GoWired/GoWired-Project/Images/GetWired.png

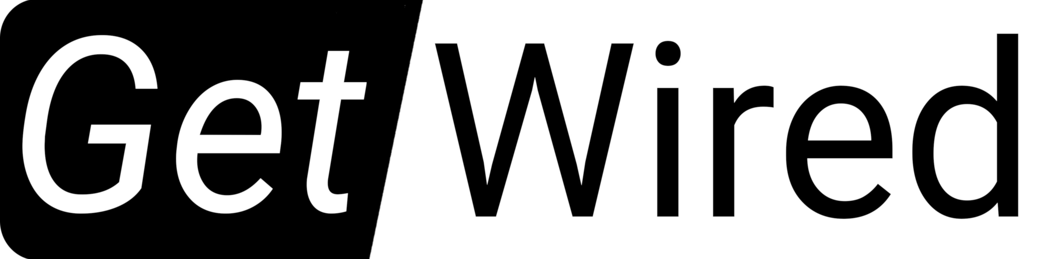
Images/GetWired.png
