GoWired/GoWired-Project/Images/Gowired-no-home-600dpi.png

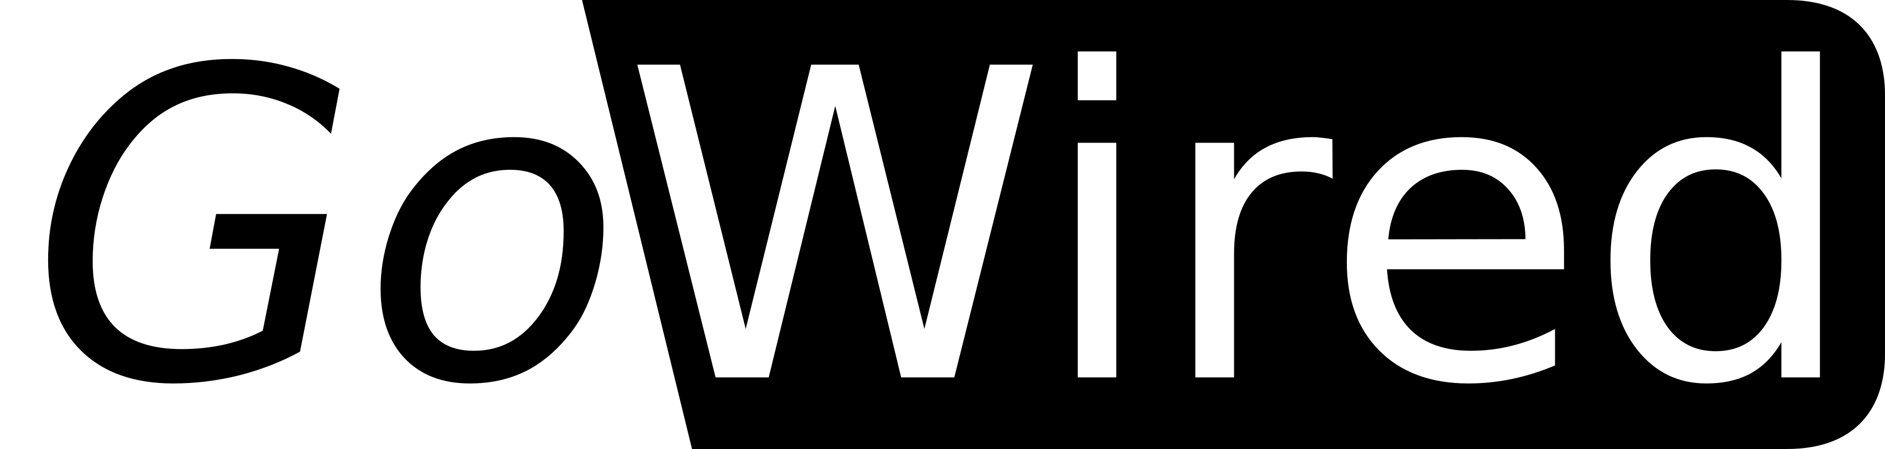
Images/Gowired-no-home-600dpi.png
