GoWired/GoWired-Project/Images/image.png

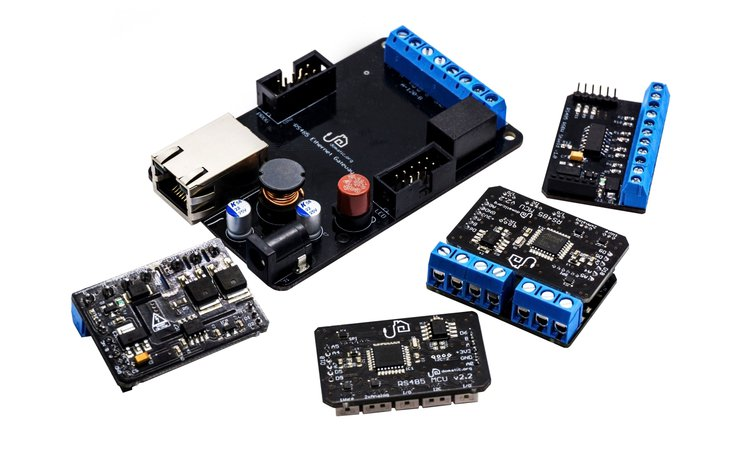
Images/image.png
