GoWired/GoWired-Project/Images/Wiring instructions.jpg

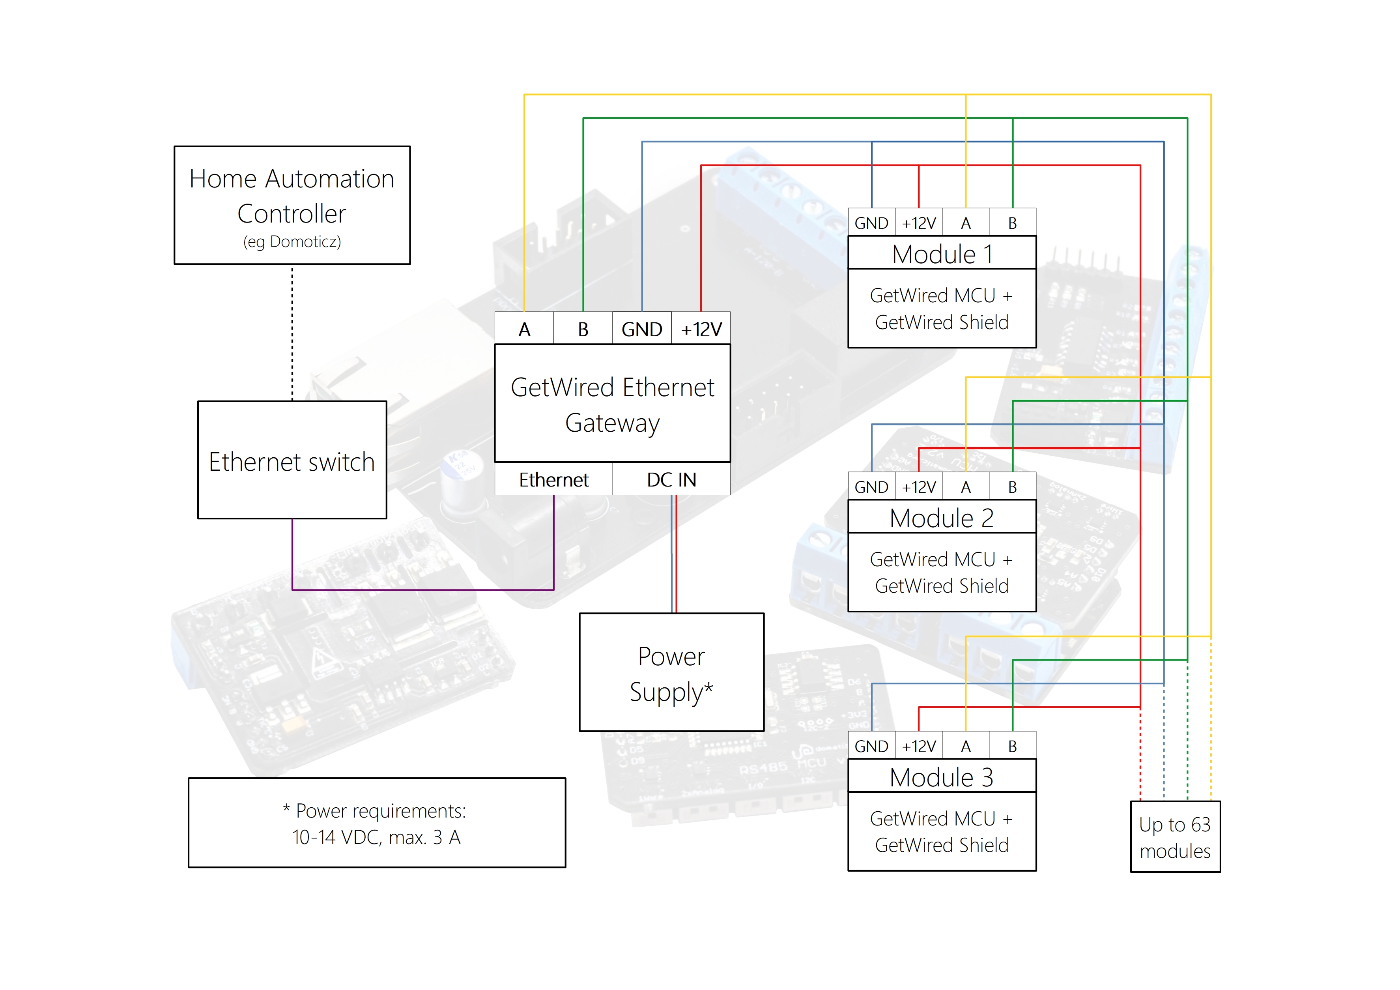
Images/Wiring instructions.jpg
