GoWired/GoWired-Project/Software/Modules/Arduino/main/main.ino

/*
 * GoWired is an open source project for WIRED home automation. It aims at making wired
 * home automation easy and affordable for every home automation enthusiast. GoWired provides
 * hardware, software, enclosures and instructions necessary to build your own bus communicating
 * smart home installation.
 * 
 * GoWired is based on RS485 industrial communication standard. The software uses MySensors
 * communication protocol (http://www.mysensors.org).
 *
 * Created by feanor-anglin
 * Copyright (C) 2018-2022 feanor-anglin
 *
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
 * ******************************
 * This is source code for GoWired MCU working with 2SSR, RGBW & 4RelayDin Shields.
 * 
 * 
 */

/***** INCLUDES *****/
#include "Configuration.h"
#include <GoWired.h>
#ifdef SHT30
  #include <SHTSensor.h>
#elif defined(DHT22)
  #include <dht.h>
#endif

/***** Globals *****/
// Shutter
#ifdef ROLLER_SHUTTER
  uint32_t MovementTime;
  uint32_t StartTime;
#endif

// Timer
uint32_t LastUpdate = 0;               // Time of last update of interval sensors
bool CheckNow = false;

// Module Safety Indicators
bool THERMAL_ERROR = false;                 // Thermal error status
bool InformControllerTS = false;            // Was controller informed about error?
bool OVERCURRENT_ERROR[4] = {false, false, false, false};             // Overcurrent error status
bool InformControllerES = false;            // Was controller informed about error?
uint8_t ET_ERROR = 3;                       // External thermometer status (0 - ok, 1 - checksum error, 2 - timeout error, 3 - default/initialization)

// Initialization
bool InitConfirm = false;

/***** Constructors *****/
// CommonIO constructor
#if (NUMBER_OF_RELAYS + NUMBER_OF_INPUTS > 0)
  CommonIO CommonIO[NUMBER_OF_RELAYS+NUMBER_OF_INPUTS];
#endif

MyMessage MsgSTATUS(0, V_STATUS);
MyMessage MsgPERCENTAGE(0, V_PERCENTAGE);
MyMessage MsgWATT(0, V_WATT);
MyMessage MsgTEMP(0, V_TEMP);
MyMessage MsgHUM(0, V_HUM);
MyMessage MsgTEXT(0, V_TEXT);

// Shutter Constructor
#ifdef ROLLER_SHUTTER
  Shutters Shutter(EEA_SHUTTER_TIME_DOWN, EEA_SHUTTER_TIME_UP, EEA_SHUTTER_POSITION);
  MyMessage MsgUP(SHUTTER_ID, V_UP);
  MyMessage MsgDOWN(SHUTTER_ID, V_DOWN);
  MyMessage MsgSTOP(SHUTTER_ID, V_STOP);
#endif

// Dimmer
#if defined(DIMMER) || defined(RGB) || defined(RGBW)
  Dimmer Dimmer;
  MyMessage MsgRGB(DIMMER_ID, V_RGB);
  MyMessage MsgRGBW(DIMMER_ID, V_RGBW);
#endif

// Power sensor constructor
#if defined(POWER_SENSOR) && !defined(FOUR_RELAY)
  PowerSensor PS;
#elif defined(POWER_SENSOR) && defined(FOUR_RELAY)
  PowerSensor PS[NUMBER_OF_RELAYS];
#endif

// Internal thermometer constructor
#ifdef INTERNAL_TEMP
  AnalogTemp AnalogTemp(IT_PIN, MAX_TEMPERATURE, MVPERC, ZEROVOLTAGE);
#endif

// External thermometer constructor
#ifdef EXTERNAL_TEMP
  #ifdef DHT22
    dht DHT;
  #endif
  #ifdef SHT30
    SHTSensor sht;
  #endif
#endif

#ifdef RS485_DEBUG
  MyMessage MsgDEBUG(DEBUG_ID, V_TEXT);
  MyMessage MsgDEBUG2(DEBUG_ID, V_WATT);
  MyMessage MsgCUSTOM(0, V_CUSTOM);
#endif

/**
 * @brief Function called before setup(); resets wdt
 * 
 */
void before() {

  #ifdef ENABLE_WATCHDOG
    wdt_reset();
    MCUSR = 0;
    wdt_disable();
  #endif
}

/**
 * @brief Setups software components: wdt, expander, inputs, outputs
 * 
 */
void setup() {

  #ifdef ENABLE_WATCHDOG
    wdt_enable(WDTO_8S);
  #endif

  float Vcc = ReadVcc();  // mV

  // POWER SENSOR
  #if defined(POWER_SENSOR) && !defined(FOUR_RELAY)
    PS.SetValues(PS_PIN, MVPERAMP, RECEIVER_VOLTAGE, MAX_CURRENT, POWER_MEASURING_TIME, Vcc);
  #elif defined(POWER_SENSOR) && defined(FOUR_RELAY)
    PS[RELAY_ID_1].SetValues(PS_PIN_1, MVPERAMP, RECEIVER_VOLTAGE, MAX_CURRENT, POWER_MEASURING_TIME, Vcc);
    PS[RELAY_ID_2].SetValues(PS_PIN_2, MVPERAMP, RECEIVER_VOLTAGE, MAX_CURRENT, POWER_MEASURING_TIME, Vcc);
    PS[RELAY_ID_3].SetValues(PS_PIN_3, MVPERAMP, RECEIVER_VOLTAGE, MAX_CURRENT, POWER_MEASURING_TIME, Vcc);
    PS[RELAY_ID_4].SetValues(PS_PIN_4, MVPERAMP, RECEIVER_VOLTAGE, MAX_CURRENT, POWER_MEASURING_TIME, Vcc);
  #endif

  // OUTPUT
  #ifdef DOUBLE_RELAY
    CommonIO[RELAY_ID_1].SetValues(RELAY_OFF, false, 4, BUTTON_1, RELAY_1);
    CommonIO[RELAY_ID_2].SetValues(RELAY_OFF, false, 4, BUTTON_2, RELAY_2);
  #endif

  #ifdef ROLLER_SHUTTER
    Shutter.SetOutputs( RELAY_OFF, RELAY_1, RELAY_2);
    CommonIO[SHUTTER_ID].SetValues(RELAY_OFF, false, 3, BUTTON_1);
    CommonIO[SHUTTER_ID + 1].SetValues(RELAY_OFF, false, 3, BUTTON_2);
    if(!Shutter.Calibrated) {
      Shutter.Calibration(UP_TIME, DOWN_TIME);
    }
  #endif

  #ifdef FOUR_RELAY
    CommonIO[RELAY_ID_1].SetValues(RELAY_OFF, 2, RELAY_1);
    CommonIO[RELAY_ID_2].SetValues(RELAY_OFF, 2, RELAY_2);
    CommonIO[RELAY_ID_3].SetValues(RELAY_OFF, 2, RELAY_3);
    CommonIO[RELAY_ID_4].SetValues(RELAY_OFF, 2, RELAY_4);
  #endif

  #if defined(DIMMER) || defined(RGB) || defined(RGBW)
    CommonIO[0].SetValues(0, false, 3, BUTTON_1);
    CommonIO[1].SetValues(0, false, 3, BUTTON_2);
  #endif

  #ifdef DIMMER
    Dimmer.SetValues(NUMBER_OF_CHANNELS, DIMMING_STEP, DIMMING_INTERVAL, LED_PIN_1, LED_PIN_2, LED_PIN_3, LED_PIN_4);
  #elif defined(RGB)
    Dimmer.SetValues(NUMBER_OF_CHANNELS, DIMMING_STEP, DIMMING_INTERVAL, LED_PIN_1, LED_PIN_2, LED_PIN_3);
  #elif defined(RGBW)
    Dimmer.SetValues(NUMBER_OF_CHANNELS, DIMMING_STEP, DIMMING_INTERVAL, LED_PIN_1, LED_PIN_2, LED_PIN_3, LED_PIN_4);
  #endif

  // INPUT
  #ifdef INPUT_1
    #ifdef PULLUP_1
      CommonIO[INPUT_ID_1].SetValues(RELAY_OFF, INVERT_1, 0, PIN_1);
    #else
      CommonIO[INPUT_ID_1].SetValues(RELAY_OFF, INVERT_1, 1, PIN_1);
    #endif
  #endif

  #ifdef INPUT_2
    #ifdef PULLUP_2
      CommonIO[INPUT_ID_2].SetValues(RELAY_OFF, INVERT_2, 0, PIN_2);
    #else
      CommonIO[INPUT_ID_2].SetValues(RELAY_OFF, INVERT_2, 1, PIN_2);
    #endif
  #endif

  #ifdef INPUT_3
    #ifdef PULLUP_3
      CommonIO[INPUT_ID_3].SetValues(RELAY_OFF, INVERT_3, 0, PIN_3);
    #else
      CommonIO[INPUT_ID_3].SetValues(RELAY_OFF, INVERT_3, 1, PIN_3);
    #endif
  #endif

  #ifdef INPUT_4
    #ifdef PULLUP_4
      CommonIO[INPUT_ID_4].SetValues(RELAY_OFF, INVERT_4, 0, PIN_4);
    #else
      CommonIO[INPUT_ID_4].SetValues(RELAY_OFF, INVERT_4, 1, PIN_4);
    #endif
  #endif

  // EXTERNAL THERMOMETER
  #ifdef EXTERNAL_TEMP
    #ifdef DHT22
      pinMode(ET_PIN, INPUT);
    #endif
    #ifdef SHT30
      Wire.begin();
      sht.init();
      sht.setAccuracy(SHTSensor::SHT_ACCURACY_MEDIUM);
    #endif
  #endif

}

/**
 * @brief Presents module to the controller, send name, software version, info about sensors
 * 
 */
void presentation() {

  sendSketchInfo(SN, SV);

  // OUTPUT
  #ifdef DOUBLE_RELAY
    present(RELAY_ID_1, S_BINARY, "Relay 1");   wait(PRESENTATION_DELAY);
    present(RELAY_ID_2, S_BINARY, "Relay 2");   wait(PRESENTATION_DELAY);
  #endif

  #ifdef ROLLER_SHUTTER
    present(SHUTTER_ID, S_COVER, "Roller Shutter");  wait(PRESENTATION_DELAY);
  #endif

  #ifdef FOUR_RELAY
    present(RELAY_ID_1, S_BINARY, "Relay 1");   wait(PRESENTATION_DELAY);
    present(RELAY_ID_2, S_BINARY, "Relay 2");   wait(PRESENTATION_DELAY);
    present(RELAY_ID_3, S_BINARY, "Relay 3");   wait(PRESENTATION_DELAY);
    present(RELAY_ID_4, S_BINARY, "Relay 4");   wait(PRESENTATION_DELAY);
  #endif

  #ifdef DIMMER
    present(DIMMER_ID, S_DIMMER, "Dimmer"); wait(PRESENTATION_DELAY);
  #endif

  #ifdef RGB
    present(DIMMER_ID, S_RGB_LIGHT, "RGB"); wait(PRESENTATION_DELAY);
  #endif

  #ifdef RGBW
    present(DIMMER_ID, S_RGBW_LIGHT, "RGBW");   wait(PRESENTATION_DELAY);
  #endif

  // DIGITAL INPUT
  #ifdef INPUT_1
    present(INPUT_ID_1, S_BINARY, "Input 1");   wait(PRESENTATION_DELAY);
  #endif

  #ifdef INPUT_2
    present(INPUT_ID_2, S_BINARY, "Input 2");   wait(PRESENTATION_DELAY);
  #endif

  #ifdef INPUT_3
    present(INPUT_ID_3, S_BINARY, "Input 3");   wait(PRESENTATION_DELAY);
  #endif

  #ifdef INPUT_4
    present(INPUT_ID_4, S_BINARY, "Input 4");   wait(PRESENTATION_DELAY);
  #endif

  #ifdef SPECIAL_BUTTON
    present(SPECIAL_BUTTON_ID, S_BINARY, "Longpress-1"); wait(PRESENTATION_DELAY);
    present(SPECIAL_BUTTON_ID+1, S_BINARY, "Longpress-2"); wait(PRESENTATION_DELAY);
  #endif

  // POWER SENSOR
  #if defined(POWER_SENSOR) && !defined(FOUR_RELAY)
    present(PS_ID, S_POWER, "Power Sensor");    wait(PRESENTATION_DELAY);
  #elif defined(POWER_SENSOR) && defined(FOUR_RELAY)
    present(PS_ID_1, S_POWER, "Power Sensor 1");    wait(PRESENTATION_DELAY);
    present(PS_ID_2, S_POWER, "Power Sensor 2");    wait(PRESENTATION_DELAY);
    present(PS_ID_3, S_POWER, "Power Sensor 3");    wait(PRESENTATION_DELAY);
    present(PS_ID_4, S_POWER, "Power Sensor 4");    wait(PRESENTATION_DELAY);
  #endif

  // Internal Thermometer
  #ifdef INTERNAL_TEMP
    present(IT_ID, S_TEMP, "Internal Thermometer"); wait(PRESENTATION_DELAY);
  #endif

  // External Thermometer
  #ifdef EXTERNAL_TEMP
    present(ETT_ID, S_TEMP, "External Thermometer"); wait(PRESENTATION_DELAY);
    present(ETH_ID, S_HUM, "External Hygrometer");  wait(PRESENTATION_DELAY);
  #endif

  // I2C


  // Error Reporting
  #ifdef ERROR_REPORTING
    #ifdef POWER_SENSOR
      present(ES_ID, S_BINARY, "OVERCURRENT ERROR");    wait(PRESENTATION_DELAY);
    #endif
    #ifdef INTERNAL_TEMP
      present(TS_ID, S_BINARY, "THERMAL ERROR");    wait(PRESENTATION_DELAY);
    #endif
    #ifdef EXTERNAL_TEMP
      present(ETS_ID, S_BINARY, "ET STATUS");   wait(PRESENTATION_DELAY);
    #endif
  #endif

  #ifdef RS485_DEBUG
    present(DEBUG_ID, S_INFO, "DEBUG INFO");
  #endif

  // Configuration sensor
  present(CONFIGURATION_SENSOR_ID, S_INFO, "TEXT Msg");

}

/**
 * @brief Sends initial value of sensors as required by Home Assistant
 * 
 */
void InitConfirmation() {

  // OUTPUT
  #ifdef DOUBLE_RELAY
    send(MsgSTATUS.setSensor(RELAY_ID_1).set(CommonIO[RELAY_ID_1].NewState));
    request(RELAY_ID_1, V_STATUS);
    wait(2000, C_SET, V_STATUS);

    send(MsgSTATUS.setSensor(RELAY_ID_2).set(CommonIO[RELAY_ID_2].NewState));
    request(RELAY_ID_2, V_STATUS);
    wait(2000, C_SET, V_STATUS);
  #endif

  #ifdef ROLLER_SHUTTER
    send(MsgUP.set(0));
    request(SHUTTER_ID, V_UP);
    wait(2000, C_SET, V_UP);

    send(MsgDOWN.set(0));
    request(SHUTTER_ID, V_DOWN);
    wait(2000, C_SET, V_DOWN);

    send(MsgSTOP.set(0));
    request(SHUTTER_ID, V_STOP);
    wait(2000, C_SET, V_STOP);

    send(MsgPERCENTAGE.setSensor(SHUTTER_ID).set(Shutter.Position));
    request(SHUTTER_ID, V_PERCENTAGE);
    wait(2000, C_SET, V_PERCENTAGE);
  #endif

  #ifdef FOUR_RELAY
    send(MsgSTATUS.setSensor(RELAY_ID_1).set(CommonIO[RELAY_ID_1].NewState));
    request(RELAY_ID_1, V_STATUS);
    wait(2000, C_SET, V_STATUS);
    
    send(MsgSTATUS.setSensor(RELAY_ID_2).set(CommonIO[RELAY_ID_2].NewState));
    request(RELAY_ID_2, V_STATUS);
    wait(2000, C_SET, V_STATUS);
    
    send(MsgSTATUS.setSensor(RELAY_ID_3).set(CommonIO[RELAY_ID_3].NewState));
    request(RELAY_ID_3, V_STATUS);
    wait(2000, C_SET, V_STATUS);
    
    send(MsgSTATUS.setSensor(RELAY_ID_4).set(CommonIO[RELAY_ID_4].NewState));
    request(RELAY_ID_4, V_STATUS);
    wait(2000, C_SET, V_STATUS);
  #endif

  #if defined(DIMMER) || defined(RGB) || defined(RGBW)
    send(MsgSTATUS.setSensor(DIMMER_ID).set(false));
    request(DIMMER_ID, V_STATUS);
    wait(2000, C_SET, V_STATUS);
    
    send(MsgPERCENTAGE.setSensor(DIMMER_ID).set(Dimmer.NewDimmingLevel));
    request(DIMMER_ID, V_PERCENTAGE);
    wait(2000, C_SET, V_PERCENTAGE);
  #endif

  #ifdef RGB
    send(MsgRGB.setSensor(DIMMER_ID).set("ffffff"));
    request(DIMMER_ID, V_RGB);
    wait(2000, C_SET, V_RGB);
  #elif defined(RGBW)
    send(MsgRGBW.setSensor(DIMMER_ID).set("ffffffff"));
    request(DIMMER_ID, V_RGBW);
    wait(2000, C_SET, V_RGBW);
  #endif

  // DIGITAL INPUT
  #ifdef INPUT_1
    send(MsgSTATUS.setSensor(INPUT_ID_1).set(CommonIO[INPUT_ID_1].NewState));
  #endif

  #ifdef INPUT_2
    send(MsgSTATUS.setSensor(INPUT_ID_2).set(CommonIO[INPUT_ID_2].NewState));
  #endif

  #ifdef INPUT_3
    send(MsgSTATUS.setSensor(INPUT_ID_3).set(CommonIO[INPUT_ID_3].NewState));
  #endif

  #ifdef INPUT_4
    send(MsgSTATUS.setSensor(INPUT_ID_4).set(CommonIO[INPUT_ID_4].NewState));
  #endif

  #ifdef SPECIAL_BUTTON
    send(MsgSTATUS.setSensor(SPECIAL_BUTTON_ID).set(0));
    send(MsgSTATUS.setSensor(SPECIAL_BUTTON_ID+1).set(0));
  #endif

  // Built-in sensors
  #ifdef POWER_SENSOR
    #if !defined(FOUR_RELAY)
      send(MsgWATT.setSensor(PS_ID).set("0"));
    #elif defined(FOUR_RELAY)
      for(int i=PS_ID_1; i<=PS_ID_4; i++)  {
        send(MsgWATT.setSensor(i).set("0"));
      }
    #endif
  #endif

  #ifdef INTERNAL_TEMP
    send(MsgTEMP.setSensor(IT_ID).set((int)AnalogTemp.MeasureT(ReadVcc())));
  #endif

  // External sensors
  #ifdef EXTERNAL_TEMP
    ETUpdate();
  #endif

  // Error Reporting
  #ifdef ERROR_REPORTING
    #ifdef POWER_SENSOR
      send(MsgSTATUS.setSensor(ES_ID).set(0));
    #endif
    #ifdef INTERNAL_TEMP
      send(MsgSTATUS.setSensor(TS_ID).set(0));
    #endif
    #ifdef EXTERNAL_TEMP
      send(MsgSTATUS.setSensor(ETS_ID).set(0));
    #endif
  #endif

  #ifdef RS485_DEBUG
    send(MsgDEBUG.setSensor(DEBUG_ID).set("DEBUG MESSAGE"));
  #endif

  send(MsgTEXT.setSensor(CONFIGURATION_SENSOR_ID).set("CONFIG INIT"));

  InitConfirm = true;
}


/**
 * @brief Handles incoming messages
 * 
 * @param message incoming message data
 */
void receive(const MyMessage &message)  {
  
  if (message.type == V_STATUS) {
    #if defined(POWER_SENSOR) && defined(ERROR_REPORTING)
      if (message.sensor == ES_ID)  {
        for (int i = 0; i < 4; i++)  {
          OVERCURRENT_ERROR[i] = message.getBool();
        }
        InformControllerES = false;
      }
    #endif
    #if defined(INTERNAL_TEMP) && defined(ERROR_REPORTING)
      if (message.sensor == TS_ID)  {
        THERMAL_ERROR = message.getBool();
        if (THERMAL_ERROR == false)  {
          InformControllerTS = false;
        }
      }
    #endif
    #ifdef SPECIAL_BUTTON
      if (message.sensor == SPECIAL_BUTTON_ID || message.sensor == SPECIAL_BUTTON_ID+1)  {
        // Ignore this message
      }
    #endif
    #if defined(DIMMER) || defined(RGB) || defined(RGBW)
      if (message.sensor == DIMMER_ID) {
        Dimmer.ChangeState(message.getBool());
      }
    #endif
    #if defined(DOUBLE_RELAY)
      if (message.sensor == RELAY_ID_1 || message.sensor == RELAY_ID_2)  {
        if (!OVERCURRENT_ERROR[0] && !THERMAL_ERROR) {
          CommonIO[message.sensor].SetState(message.getBool());
          CommonIO[message.sensor].SetRelay();
        }
      }
    #endif
    #ifdef FOUR_RELAY
      if (message.sensor >= RELAY_ID_1 && message.sensor < NUMBER_OF_RELAYS) {
        for (int i = RELAY_ID_1; i < RELAY_ID_1 + NUMBER_OF_RELAYS; i++) {
          if (message.sensor == i) {
            if (!OVERCURRENT_ERROR[i] && !THERMAL_ERROR) {
              CommonIO[message.sensor].NewState = message.getBool();
              CommonIO[message.sensor].SetRelay();
            }
          }
        }
      }
    #endif
  }
  else if (message.type == V_PERCENTAGE) {
    #ifdef ROLLER_SHUTTER
      if(message.sensor == SHUTTER_ID) {
        int NewPosition = atoi(message.data);
        NewPosition = NewPosition > 100 ? 100 : NewPosition;
        NewPosition = NewPosition < 0 ? 0 : NewPosition;
        Shutter.NewState = 2;
        ShutterUpdate(0);
        MovementTime = Shutter.ReadNewPosition(NewPosition) * 10;
      }
    #endif
    #if defined(DIMMER) || defined(RGB) || defined(RGBW)
      if(message.sensor == DIMMER_ID) {
        Dimmer.NewDimmingLevel = atoi(message.data);
        Dimmer.NewDimmingLevel = Dimmer.NewDimmingLevel > 100 ? 100 : Dimmer.NewDimmingLevel;
        Dimmer.NewDimmingLevel = Dimmer.NewDimmingLevel < 0 ? 0 : Dimmer.NewDimmingLevel;
      }
    #endif
  }
  else if (message.type == V_RGB || message.type == V_RGBW) {
    #if defined(RGB) || defined(RGBW)
      if(message.sensor == DIMMER_ID) {
        const char *rgbvalues = message.getString();

        Dimmer.NewColorValues(rgbvalues);
      }
    #endif
  }
  else if(message.type == V_UP) {
    #ifdef ROLLER_SHUTTER
      if(message.sensor == SHUTTER_ID) {
        MovementTime = Shutter.ReadMessage(0) * 1000;
      }
    #endif
  }
  else if(message.type == V_DOWN) {
    #ifdef ROLLER_SHUTTER
      if(message.sensor == SHUTTER_ID) {
        MovementTime = Shutter.ReadMessage(1) * 1000;
      }
    #endif
  }
  else if(message.type == V_STOP) {
    #ifdef ROLLER_SHUTTER
      if(message.sensor == SHUTTER_ID) {
        MovementTime = Shutter.ReadMessage(2);
      }
    #endif
  }
  else if(message.type == V_TEXT) {
    // Configuration by message
    if(message.sensor == CONFIGURATION_SENSOR_ID)  {
      
      // Initialize strings and pointers
      char ReceivedPayload[10];
      char *RPaddr = ReceivedPayload;
      String RPstr = String(message.getString());

      // Turn String payload to char array and send back to the controller
      RPstr.toCharArray(ReceivedPayload, 10);
      send(MsgTEXT.setSensor(CONFIGURATION_SENSOR_ID).set(RPaddr));

      if(RPstr.equals(CONF_MSG_1)) {
        #ifdef ROLLER_SHUTTER
          // Roller shutter: calibration
          float Vcc = ReadVcc();
          ShutterCalibration(Vcc);
        #endif
      }
      else if(RPstr.equals(CONF_MSG_2)) {
        // No effect
      }
      else if(RPstr.equals(CONF_MSG_3)) {
        // Watchdog test procedure / module restart
        delay(10000);
      }
      else if(RPstr.equals(CONF_MSG_4)) {
        // Clear EEPROM and restart
        for (int i=0;i<1024;i++) {
          EEPROM.write(i,0xFF);
        }
        delay(10000);
      }
    }
  }
}

/**
 * @brief Reads temperature & humidity from an optional, external thermometer 
 * 
 */
void ETUpdate()  {

  #ifdef EXTERNAL_TEMP
    #ifdef DHT22
      int chk = DHT.read22(ET_PIN);
      switch (chk)  {
        case DHTLIB_OK:
          send(MsgTEMP.setSensor(ETT_ID).setDestination(0).set(DHT.temperature, 1));
          send(MsgHUM.setSensor(ETH_ID).set(DHT.humidity, 1));
          #ifdef HEATING_SECTION_SENSOR
            send(MsgTEMP.setSensor(ETT_ID).setDestination(MY_HEATING_CONTROLLER).set(DHT.temperature, 1));
          #endif
          #ifdef ERROR_REPORTING
            if (ET_ERROR != 0) {
              ET_ERROR = 0;
              send(MsgSTATUS.setSensor(ETS_ID).set(ET_ERROR));
            }
          #endif
        break;
        case DHTLIB_ERROR_CHECKSUM:
          #ifdef ERROR_REPORTING
            ET_ERROR = 1;
            send(MsgSTATUS.setSensor(ETS_ID).set(ET_ERROR));
          #endif
        break;
        case DHTLIB_ERROR_TIMEOUT:
          #ifdef ERROR_REPORTING
            ET_ERROR = 2;
            send(MsgSTATUS.setSensor(ETS_ID).set(ET_ERROR));
          #endif
        break;
        default:
          #ifdef ERROR_REPORTING
            ET_ERROR = 3;
            send(MsgSTATUS.setSensor(ETS_ID).set(ET_ERROR));
          #endif
        break;
      }
    #elif defined(SHT30)
      if(sht.readSample())  {
        send(MsgTEMP.setSensor(ETT_ID).setDestination(0).set(sht.getTemperature(), 1));
        send(MsgHUM.setSensor(ETH_ID).set(sht.getHumidity(), 1));
        #ifdef HEATING_SECTION_SENSOR
          send(MsgTEMP.setSensor(ETT_ID).setDestination(MY_HEATING_CONTROLLER).set(sht.getTemperature(), 1));
        #endif
      }
      else  {
        #ifdef ERROR_REPORTING
          ET_ERROR = 1;
          send(MsgSTATUS.setSensor(ETS_ID).set(ET_ERROR));
        #endif
      }
    #endif
  #endif
}

/**
 * @brief Updates CommonIO class objects; reads inputs & set outputs
 * 
 */
void UpdateIO() {

  int FirstSensor = 0;
  int Iterations = NUMBER_OF_RELAYS+NUMBER_OF_INPUTS;

  if(Iterations <= 0)  return;

  for (int i = FirstSensor; i < FirstSensor + Iterations; i++)  {
    CommonIO[i].CheckInput(LONGPRESS_DURATION, DEBOUNCE_VALUE);

    if (CommonIO[i].NewState == CommonIO[i].State)  continue;

    switch(CommonIO[i].SensorType)  {
      case 0:
        // Door/window/button
      case 1:
        // Motion sensor
        send(MsgSTATUS.setSensor(i).set(CommonIO[i].NewState));
        CommonIO[i].State = CommonIO[i].NewState;
        break;
      case 2:
        // Relay output
        // Nothing to do here
        break;
      case 3:
        // Button input
        #ifdef DIMMER_ID
          if(i == 0)  {
            if(CommonIO[i].NewState != 2) {
              // Change dimmer state
              Dimmer.ChangeState(!Dimmer.CurrentState);
              send(MsgSTATUS.setSensor(DIMMER_ID).set(Dimmer.CurrentState));
              CommonIO[i].State = CommonIO[i].NewState;
            }
            if(CommonIO[i].NewState == 2) {
              #ifdef SPECIAL_BUTTON
                send(MsgSTATUS.setSensor(SPECIAL_BUTTON_ID).set(true));
              #endif
              CommonIO[i].NewState = CommonIO[i].State;
            }
          }
          else if(i == 1) {
            if(CommonIO[i].NewState != 2)  {
              if(!Dimmer.CurrentState) continue;
                    
              // Toggle dimming level by DIMMING_TOGGLE_STEP
              Dimmer.NewDimmingLevel += DIMMING_TOGGLE_STEP;
              Dimmer.NewDimmingLevel = Dimmer.NewDimmingLevel > 100 ? DIMMING_TOGGLE_STEP : Dimmer.NewDimmingLevel;
              send(MsgPERCENTAGE.setSensor(DIMMER_ID).set(Dimmer.NewDimmingLevel));
              CommonIO[i].NewState = CommonIO[i].State;
            }
          }
        #endif
        #ifdef ROLLER_SHUTTER
          if(CommonIO[i].NewState != 2)  {
            MovementTime = Shutter.ReadButtons(i) * 1000;
            CommonIO[i].State = CommonIO[i].NewState;
          }
          else  {
            #ifdef SPECIAL_BUTTON
              send(MsgSTATUS.setSensor(SPECIAL_BUTTON_ID).set(true));
            #endif
            CommonIO[i].NewState = CommonIO[i].State;
          }
        #endif
        break;
      case 4:
        // Button input + Relay output
        if (CommonIO[i].NewState != 2)  {
          if (OVERCURRENT_ERROR[0] || THERMAL_ERROR)  continue;

          CommonIO[i].SetRelay();
          send(MsgSTATUS.setSensor(i).set(CommonIO[i].NewState));
        }
        else if (CommonIO[i].NewState == 2)  {
          #ifdef SPECIAL_BUTTON
            uint8_t SensorID = i == 0 ? SPECIAL_BUTTON_ID : SPECIAL_BUTTON_ID+1;
            send(MsgSTATUS.setSensor(SensorID).set(true));
          #endif
          
          CommonIO[i].NewState = CommonIO[i].State;
        }
        break;
      default:
        // Nothing to do here
        break;
    }
  }
}

/**
 * @brief Measures shutter movement duration; calls class Calibration() function to save measured durations
 * 
 * @param Vcc current uC voltage
 */
void ShutterCalibration(float Vcc)  {

  #ifdef ROLLER_SHUTTER

  float Current = 0;
  uint32_t DownTimeCumulated = 0;
  uint32_t UpTimeCumulated = 0;
  uint32_t StartTime = 0;
  uint32_t StopTime = 0;
  uint32_t MeasuredTime = 0;

  // Opening the shutter  
  Shutter.NewState = 0;
  Shutter.Movement();

  do  {
    delay(500);
    wdt_reset();
    Current = PS.MeasureAC(Vcc);
  } while(Current > PS_OFFSET);

  Shutter.NewState = 2;
  Shutter.Movement();

  delay(1000);

  // Calibrating
  for(int i=0; i<CALIBRATION_SAMPLES; i++) {
    for(int j=1; j>=0; j--)  {
      Shutter.NewState = j;
      Shutter.Movement();
      StartTime = millis();

      do  {
        delay(250);
        Current = PS.MeasureAC(Vcc);
        StopTime = millis();
        wdt_reset();
      } while(Current > PS_OFFSET);

      Shutter.NewState = 2;
      Shutter.Movement();

      MeasuredTime = StopTime - StartTime;

      if(j) {
        DownTimeCumulated += (int)(MeasuredTime / 1000);
      }
      else  {
        UpTimeCumulated += (int)(MeasuredTime / 1000);
      }

      delay(1000);
    }
  }

  Shutter.Position = 0;

  uint8_t DownTime = (int)(DownTimeCumulated / CALIBRATION_SAMPLES);
  uint8_t UpTime = (int)(UpTimeCumulated / CALIBRATION_SAMPLES);

  Shutter.Calibration(UpTime+1, DownTime+1);

  EEPROM.put(EEA_SHUTTER_TIME_DOWN, DownTime);
  EEPROM.put(EEA_SHUTTER_TIME_UP, UpTime);
  EEPROM.put(EEA_SHUTTER_POSITION, Shutter.Position);

  // Inform Controller about the current state of roller shutter
  send(MsgSTOP);
  send(MsgPERCENTAGE.setSensor(SHUTTER_ID).set(Shutter.Position));
  #ifdef RS485_DEBUG
    send(MsgDEBUG.set("DownTime ; UpTime"));
    send(MsgCUSTOM.set(DownTime)); send(MsgCUSTOM.set(UpTime));
  #endif

  #endif
    
}

/**
 * @brief Updates shutter condition, informs controller about shutter condition and position
 * 
 */
void ShutterUpdate(float Current) {

  #ifdef ROLLER_SHUTTER

  uint32_t StopTime = 0;
  uint32_t MeasuredTime;
  uint8_t TempState = 2;
  bool Direction;

  if(Shutter.State != 2) {
    if((millis() >= StartTime + MovementTime) || (Current < PS_OFFSET)) {
      StopTime = millis();
    }
    else if(millis() < StartTime)  {
      uint32_t Temp = 4294967295 - StartTime + millis();
      wait(MovementTime - Temp);
      StartTime = 0;
      StopTime = MovementTime;
    }
  }

  if(Shutter.State != Shutter.NewState) {
    if(Shutter.NewState != 2)  {
      if(Shutter.State == 2)  {
        ShutterStart();
      }
      else  {
        TempState = Shutter.NewState;
        StopTime = millis();
      }
    }
    else  {
      StopTime = millis();
    }
  }

  if(StopTime > 0)  {
    Direction = Shutter.State;
    Shutter.NewState = 2;
    Shutter.Movement();
    send(MsgSTOP.setSensor(SHUTTER_ID));

    MeasuredTime = StopTime - StartTime;
    Shutter.CalculatePosition(Direction, MeasuredTime);
    EEPROM.put(EEA_SHUTTER_POSITION, Shutter.Position);
  
    send(MsgPERCENTAGE.setSensor(SHUTTER_ID).set(Shutter.Position));
  
    if(TempState != 2)  {
      wait(500);
      Shutter.NewState = TempState;
      ShutterStart();
    }
  }
  #endif
}

void ShutterStart() {

  #ifdef ROLLER_SHUTTER

  Shutter.Movement();
  StartTime = millis();

  Shutter.NewState == 0 ? send(MsgUP.setSensor(SHUTTER_ID)) : send(MsgDOWN.setSensor(SHUTTER_ID));

  wait(500);

  #endif
}

/**
 * @brief Informs controller about power sensor readings
 * 
 * @param Current current measured by sensor 
 * @param Sensor sensor ID if more than one sensor is attached
 */
void PSUpdate(float Current, uint8_t Sensor = 0)  {

  if(Current == 0 && PS.OldValue == 0)  return;
  else if(Current < 1 && (abs(PS.OldValue - Current) < 0.1)) return;
  else if(Current >= 1 && (abs(PS.OldValue - Current) < (0.1 * PS.OldValue))) return;
  
  #if defined(POWER_SENSOR) && !defined(FOUR_RELAY)
    send(MsgWATT.setSensor(PS_ID).set(PS.CalculatePower(Current, COSFI), 0));
    PS.OldValue = Current;
  #elif defined(POWER_SENSOR) && defined(FOUR_RELAY)
    send(MsgWATT.setSensor(Sensor+4).set(PS[Sensor].CalculatePower(Current, COSFI), 0));
    PS[Sensor].OldValue = Current;
  #endif

}

/**
 * @brief Measures uC supply voltage
 * 
 * @return long measured voltage in mV
 */
long ReadVcc() {
  
  long result;
  
  // Read 1.1V reference against AVcc
  ADMUX = _BV(REFS0) | _BV(MUX3) | _BV(MUX2) | _BV(MUX1);
  
  delay(2);
  
  ADCSRA |= _BV(ADSC); // Convert
  
  while (bit_is_set(ADCSRA,ADSC));
  
  result = ADCL;
  result |= ADCH<<8;
  result = 1126400L / result; // Back-calculate AVcc in mV
  result = result;
  
  return result;
}

/**
 * @brief main loop: calls all 'Update' functions, runs all measurements, checks if safety parameters are within limits
 * 
 */
void loop() {

  float Vcc = ReadVcc(); // mV
  float Current = 0;

  // Sending out states for the first time (as required by Home Assistant)
  if (!InitConfirm)  {
    InitConfirmation();
  }

  // Reading power sensor(s)
  #if defined(POWER_SENSOR) && !defined(FOUR_RELAY)
    #if defined(DOUBLE_RELAY) || defined(ROLLER_SHUTTER)
      if (digitalRead(RELAY_1) == RELAY_ON || digitalRead(RELAY_2) == RELAY_ON)  {
        Current = PS.MeasureAC(Vcc);
      }
    #elif defined(DIMMER) || defined(RGB) || defined(RGBW)
      if (Dimmer.CurrentState)  {
        Current = PS.MeasureDC(Vcc);
      }
    #endif
      
    #ifdef ERROR_REPORTING
      OVERCURRENT_ERROR[0] = PS.ElectricalStatus(Current);
    #endif
    
    PSUpdate(Current);

  #elif defined(POWER_SENSOR) && defined(FOUR_RELAY)
    for (int i = RELAY_ID_1; i < RELAY_ID_1 + NUMBER_OF_RELAYS; i++) {
      if (CommonIO[i].State == RELAY_ON)  {
        Current = PS[i].MeasureAC(Vcc);
      }
      else  {
        Current = 0;
      }
      #ifdef ERROR_REPORTING
        OVERCURRENT_ERROR[i] = PS[i].ElectricalStatus(Current);
      #endif

      PSUpdate(Current, i);
    }
  #endif

  // Current safety
  #if defined(ERROR_REPORTING) && defined(POWER_SENSOR)
    #ifdef FOUR_RELAY
      for (int i = RELAY_ID_1; i < RELAY_ID_1 + NUMBER_OF_RELAYS; i++)  {
        if (OVERCURRENT_ERROR[i]) {
          // Current to high
          CommonIO[i].NewState = RELAY_OFF;
          CommonIO[i].SetRelay();
          send(MsgSTATUS.setSensor(i).set(CommonIO[i].NewState));
          send(MsgSTATUS.setSensor(ES_ID).set(OVERCURRENT_ERROR[i]));
          InformControllerES = true;
        }
        else if(!OVERCURRENT_ERROR[i] && InformControllerES) {
          // Current normal (only after reporting error)
          send(MsgSTATUS.setSensor(ES_ID).set(OVERCURRENT_ERROR[i]));
          InformControllerES = false;
        }
      }
    #else
      if(OVERCURRENT_ERROR[0])  {
        // Current to high
        #ifdef DOUBLE_RELAY
          for (int i = RELAY_ID_1; i < RELAY_ID_1 + NUMBER_OF_RELAYS; i++)  {
            CommonIO[i].NewState = RELAY_OFF;
            CommonIO[i].SetRelay();
            send(MsgSTATUS.setSensor(i).set(CommonIO[i].NewState));
          }
        #elif defined(ROLLER_SHUTTER)
          Shutter.NewState = 2;
          ShutterUpdate(0);
        #elif defined(DIMMER) || defined(RGB) || defined(RGBW)
          //Dimmer.NewState = false;
          Dimmer.ChangeState(false);
          send(MsgSTATUS.setSensor(DIMMER_ID).set(Dimmer.CurrentState));
        #endif

        send(MsgSTATUS.setSensor(ES_ID).set(OVERCURRENT_ERROR[0]));
        InformControllerES = true;
      }
      else if(!OVERCURRENT_ERROR[0] && InformControllerES)  {
        // Current normal (only after reporting error)
        send(MsgSTATUS.setSensor(ES_ID).set(OVERCURRENT_ERROR[0]));
        InformControllerES = false;
      }
    #endif
  #endif

  // Reading internal temperature sensor
  #if defined(ERROR_REPORTING) && defined(INTERNAL_TEMP)
    THERMAL_ERROR = AnalogTemp.ThermalStatus(AnalogTemp.MeasureT(Vcc));
  #endif

  // Thermal safety
  #if defined(ERROR_REPORTING) && defined(INTERNAL_TEMP)
    if (THERMAL_ERROR && !InformControllerTS) {
    // Board temperature to high
      #ifdef DOUBLE_RELAY
        for (int i = RELAY_ID_1; i < RELAY_ID_1 + NUMBER_OF_RELAYS; i++)  {
          CommonIO[i].NewState = RELAY_OFF;
          CommonIO[i].SetRelay();
          send(MsgSTATUS.setSensor(i).set(CommonIO[i].NewState));
        }
      #elif defined(ROLLER_SHUTTER)
        Shutter.NewState = 2;
        ShutterUpdate(0);
      #elif defined(DIMMER) || defined(RGB) || defined(RGBW)
        //Dimmer.NewState = false;
        Dimmer.ChangeState(false);
        send(MsgSTATUS.setSensor(DIMMER_ID).set(Dimmer.CurrentState));
      #endif
      send(MsgSTATUS.setSensor(TS_ID).set(THERMAL_ERROR));
      InformControllerTS = true;
      CheckNow = true;
    }
    else if (!THERMAL_ERROR && InformControllerTS) {
      send(MsgSTATUS.setSensor(TS_ID).set(THERMAL_ERROR));
      InformControllerTS = false;
    }
  #endif

  // Reading inputs / activating outputs
  if (NUMBER_OF_RELAYS + NUMBER_OF_INPUTS > 0) {
    UpdateIO();
  }

  // Updating roller shutter
  #ifdef ROLLER_SHUTTER
    ShutterUpdate(Current);
  #endif

  #if defined(DIMMER) || defined(RGB) || defined(RGBW)
    Dimmer.UpdateDimmer();
  #endif

  // Reset LastUpdate if millis() has overflowed
  if(LastUpdate > millis()) {
    LastUpdate = millis();
  }  
  
  // Checking out sensors which report at a defined interval
  if ((millis() > LastUpdate + INTERVAL) || CheckNow == true)  {
    #ifdef INTERNAL_TEMP
      send(MsgTEMP.setSensor(IT_ID).set((int)AnalogTemp.MeasureT(Vcc)));
    #endif
    #ifdef EXTERNAL_TEMP
      ETUpdate();
    #endif
    LastUpdate = millis();
    CheckNow = false;
  }

  wait(LOOP_TIME);
}
/*

   EOF

*/
