GoWired/GoWired-Project/GetWired New Firmware/UniversalInput.h

/*
 * UniversalInput.h
 * 
 * SensorType:
 * 0 - INPUT_PULLUP sensor
 * 1 - INPUT sensor
 * 2 - Relay output
 * 3 - Button input
 * 4 - Button input + Relay output
 *
 */

#ifndef UniversalInput_h
#define UniversalInput_h

#include "Arduino.h"


class UniversalInput
{
  public:
    UniversalInput();       

    uint8_t SensorType;
    uint8_t NewState;
    uint8_t OldState;

    void SetValues(bool RelayOFF, uint8_t Type, uint8_t Pin1, uint8_t Pin2=0);
    void CheckInput();
    void SetRelay();
  
  private:
    uint8_t _RelayPin;
    uint8_t _SensorPin;
    bool _LowStateDetection;
    bool _HighStateDetection;
    bool _Condition;
    bool _RelayOFF;
   
};

#endif
